mattnkrueger/microcontroller-game-console/3d_models/FINAL_inside_plate.stl

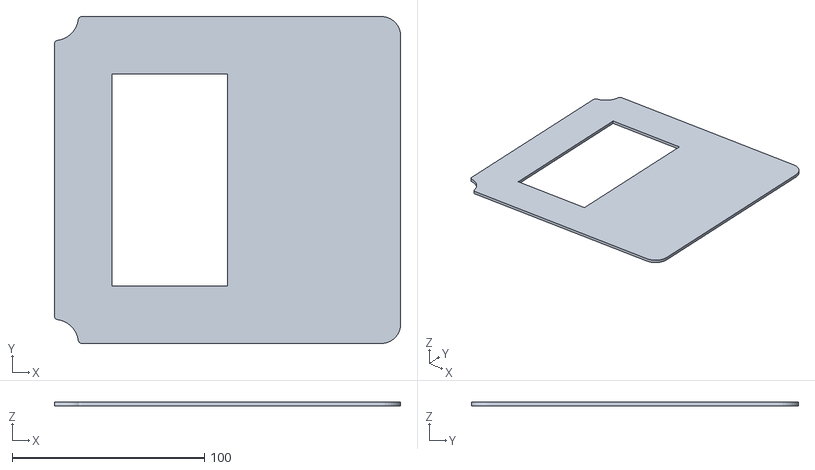
[picture p30: CAD file, 2025-05-08]
3d_models/FINAL_inside_plate.stl
180.0 x 170.0 x 2.00
