mattnkrueger/microcontroller-game-console/3d_models/FINAL_rpg_cap_2mm.stl

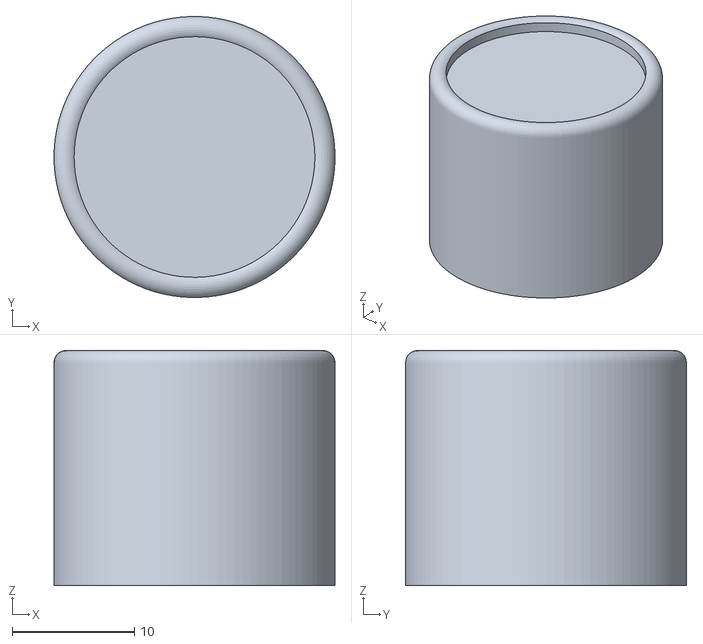
[picture p31: CAD file, 2025-05-08]
3d_models/FINAL_rpg_cap_2mm.stl
23.0 x 23.0 x 19.2
