mattnkrueger/microcontroller-game-console/3d_models/FINAL_controller_top.stl

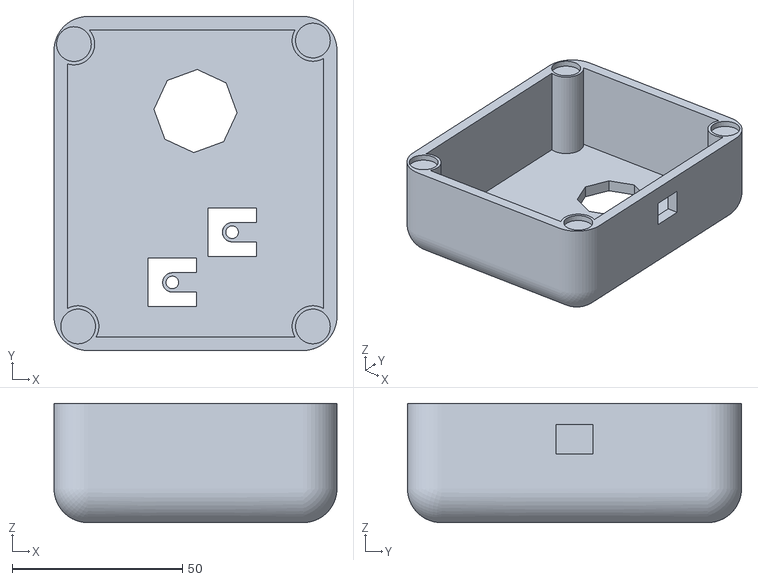
[picture p32: CAD file, 2025-05-08]
3d_models/FINAL_controller_top.stl
83.0 x 98.0 x 35.0
