mattnkrueger/microcontroller-game-console/KiCAD/Final_Project_Schematic.kicad_sch

## KiCad design KiCAD/Final_Project_Schematic.kicad_sch (2025-05-08)

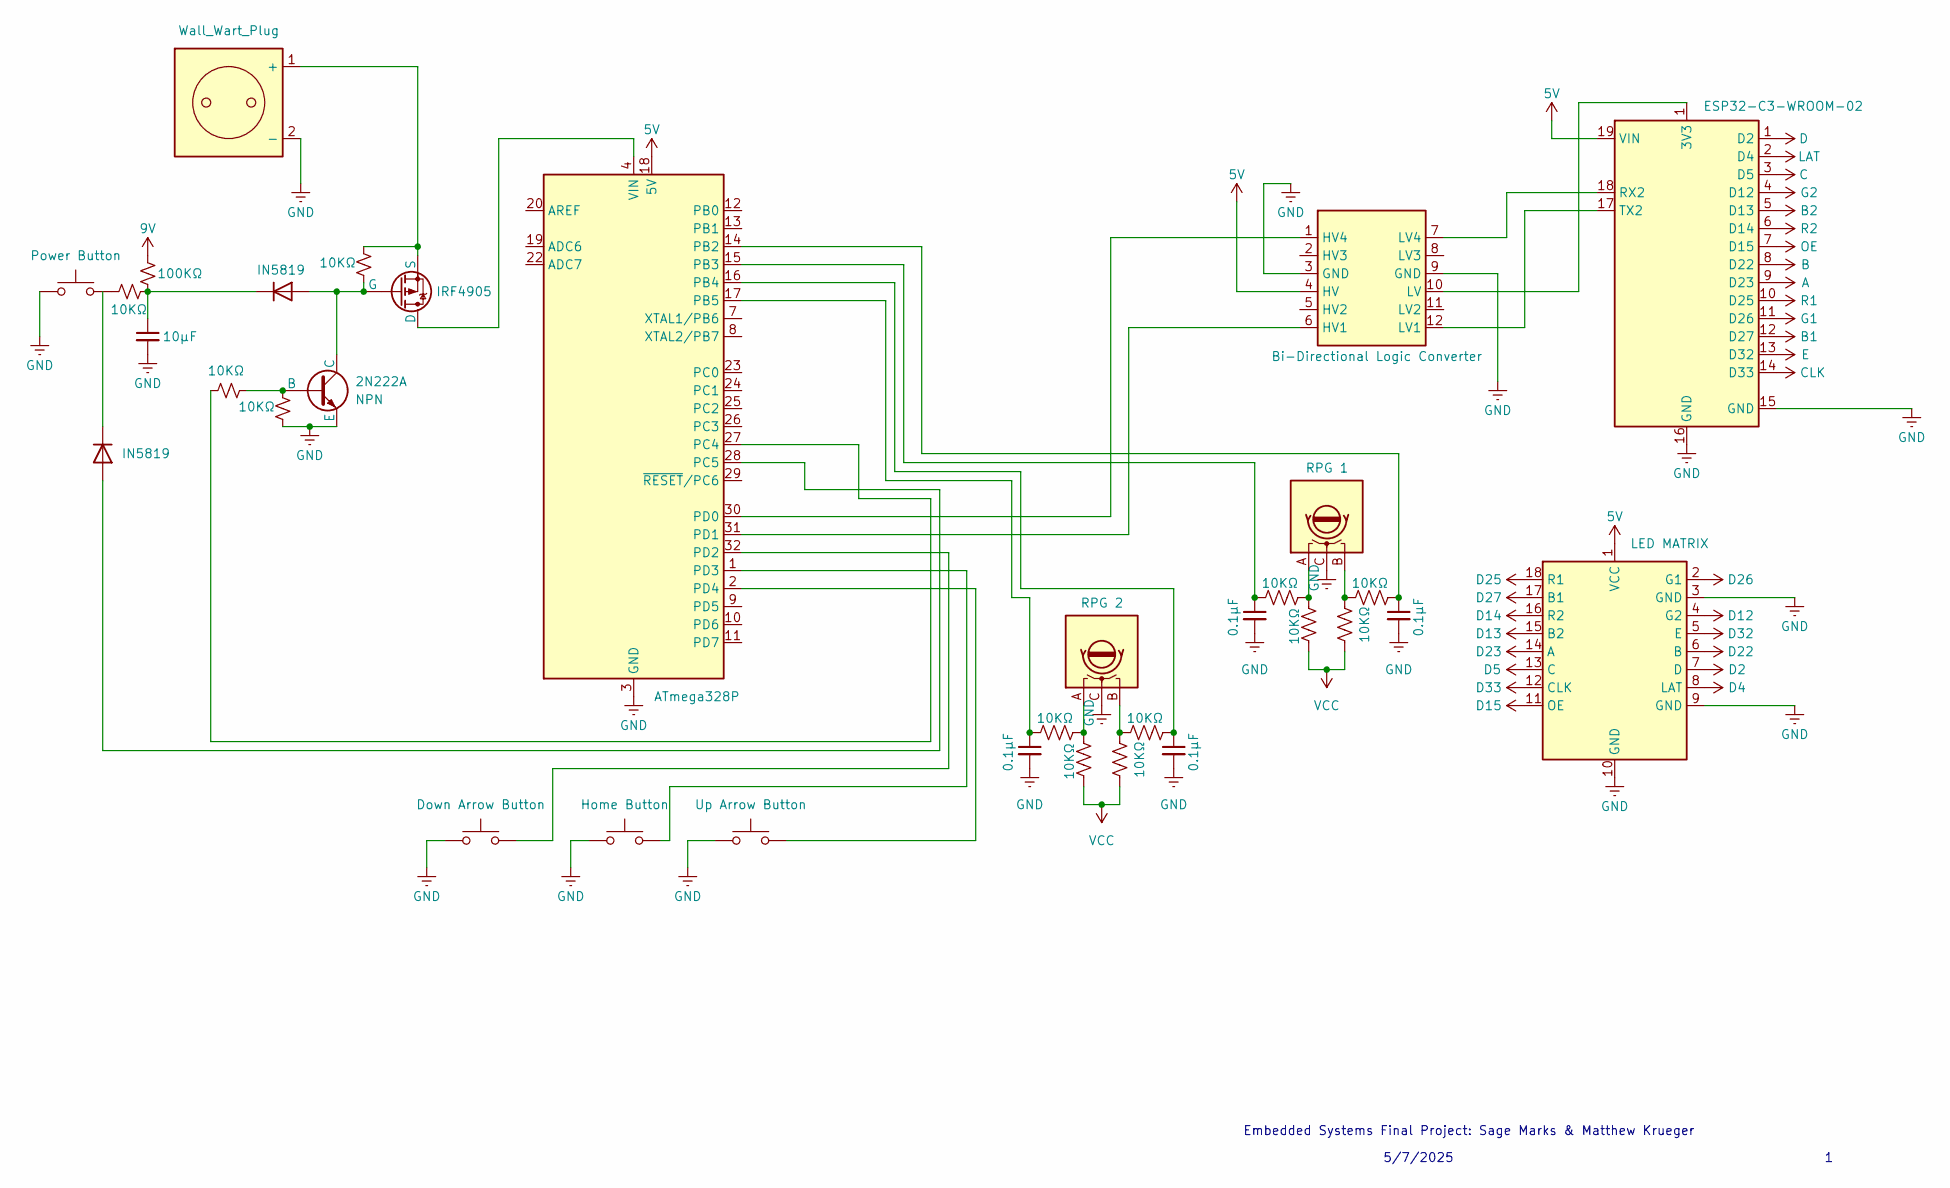
[picture p34: schematic Final_Project_Schematic.kicad_sch]

Parts:
2N222A: NPN
10KΩ, 100KΩ: R_Small_US
C1: 10µF
C2, C3, C4, C5: 0.1µF
D1, D2: IN5819
IRF4905: PMOS
P1: Wall_Wart_Plug
R3, R4, R5, R6, R7, R8, R9, R10: 10KΩ
SW1: Power Button
SW2: RPG 1
SW3: RPG 2
SW4: Home Button
SW5: Up Arrow Button
SW6: Down Arrow Button
U1: ATmega328P; TQFP-32_7x7mm_P0.8mm
U2: ESP32-C3-WROOM-02
U3: Bi-Directional Logic Converter; TSSOP-16_4.4x5mm_P0.65mm
U4: LED MATRIX; SOP-24_7.5x15.4mm_P1.27mm

Connections:
5V: U1.18 (5V), U2.19 (VIN), U3.4 (HV), U4.1 (VCC)
9V: 100KΩ.1
A: U2.9 (D23)
B: U2.8 (D22)
B1: U2.12 (D27)
B2: U2.5 (D13)
C: U2.3 (D5)
CLK: U2.14 (D33)
D: U2.1 (3V3)
D2: U4.7 (D)
D4: U4.8 (LAT)
D5: U4.13 (C)
D12: U4.4 (G2)
D13: U4.15 (B2)
D14: U4.16 (R2)
D15: U4.11 (OE)
D22: U4.6 (B)
D23: U4.14 (A)
D25: U4.18 (R1)
D26: U4.2 (G1)
D27: U4.17 (B1)
D32: U4.5 (E)
D33: U4.12 (CLK)
E: U2.13 (D32)
G1: U2.11 (D26)
G2: U2.4 (D12)
GND: 2N222A.3 (E), 10KΩ.2, C1.2, C2.2, C3.2, C4.2, C5.2, P1.2 (-), SW1.1, SW2.C, SW3.C, SW4.1, SW5.1, SW6.1, U1.3 (GND), U1.5 (GND), U1.21 (GND), U2.15 (GND), U2.16 (GND), U3.3 (GND), U3.9 (GND), U4.3 (GND), U4.9 (GND), U4.10 (GND)
LAT: U2.2 (D4)
unnamed: 2N222A.2 (B), 10KΩ.1, IRF4905.1 (S), P1.1 (+)
unnamed: 2N222A.1 (C), 10KΩ.2, D1.2 (A), IRF4905.2 (G), SW1.2, U1.27 (PC4)
unnamed: 10KΩ.1, 100KΩ.2, C1.1, D1.1 (K)
unnamed: C2.1, R5.2, U1.15 (PB3)
unnamed: C3.1, R6.1, U1.14 (PB2)
unnamed: C4.1, R7.2, U1.17 (PB5)
unnamed: C5.1, R10.1, U1.16 (PB4)
unnamed: D2.2 (A), U1.28 (PC5)
unnamed: IRF4905.3 (D), U1.4 (VIN), U1.6 (VCC)
unnamed: R3.1, R5.1, SW2.A
unnamed: R4.1, R6.2, SW2.B
unnamed: R7.1, R8.1, SW3.A
unnamed: R9.1, R10.2, SW3.B
unnamed: SW4.2, U1.1 (PD3)
unnamed: SW5.2, U1.2 (PD4)
unnamed: SW6.2, U1.32 (PD2)
unnamed: U1.30 (PD0), U3.1 (HV4)
unnamed: U1.31 (PD1), U3.6 (HV1)
unnamed: U2.1 (3V3), U3.10 (LV)
unnamed: U2.17 (TX2), U3.12 (LV1)
unnamed: U2.18 (RX2), U3.7 (LV4)
OE: U2.7 (D15)
R1: U2.10 (D25)
R2: U2.6 (D14)
VCC: R3.2, R4.2, R8.2, R9.2

Notes on the sheet:
Embedded Systems Final Project: Sage Marks & Matthew Krueger
5/7/2025
